fluffyfreak/tf330/rtl/ata.v

`timescale 1ns / 1ps
/*
    Copyright (C) 2016-2017, Stephen J. Leary
    All rights reserved.
    
    This file is part of  TF530 (Terrible Fire 030 Accelerator).

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
    You should have received a copy of the GNU General Public License
    along with TF530. If not, see <http://www.gnu.org/licenses/>.
*/

module ata (
           input         CLK,
           input         AS,
           input         RW,
           input [31:0] A,
           input        WAIT,

           output [1:0] IDECS,
           output        IOR,
           output        IOW,
           output   DTACK,
           output        ACCESS

       );

/* Timing Diagram
                 S0 S1 S2 S3 S4 S5  W  W S6 S7
     __    __    __    __    __    __    __    __    __    __    __    __   
CLK |  |__|  |__|  |__|  |__|  |__|  |__|  |__|  |__|  |__|  |__|  |__|  |__
     _________________                         _____________________________
AS                    \\\_____________________/
    _______________                            _____________________________
CS                 \__________________________/
    ______________________                     _____________________________
IOR                       \___________________/
    _____________________________        ___________________________________
IOW                              \______/
    _____________________________        ___________________________________
DTACK                            \______/     
    _________________________       ________________________________________
WAIT                         \_____/
        
*/

// decode directly from AS and Address Bus.
wire GAYLE_IDE = ({A[31:15]} != {16'h00DA,1'b0});

reg ASDLY = 1'b1;
reg ASDLY2 = 1'b1;
reg DTACK_INT = 1'b1;

reg IOR_INT = 1'b1;
reg IOW_INT = 1'b1;

always @(posedge CLK or posedge AS) begin

    if (AS == 1'b1) begin

        ASDLY <= 1'b1;
        ASDLY2 <= 1'b1;

    end else begin

        ASDLY <= AS;
        ASDLY2 <= ASDLY;

    end

end

always @(negedge CLK or posedge AS) begin

    if (AS == 1'b1) begin

        IOR_INT <= 1'b1;
        IOW_INT <= 1'b1;
        DTACK_INT <= 1'b1;

    end else begin

        IOR_INT <= ~RW | ASDLY | GAYLE_IDE;
        IOW_INT <=  RW | ASDLY2 | GAYLE_IDE;
        DTACK_INT <=  ASDLY2 | GAYLE_IDE;

    end

end

assign IOR = IOR_INT;
assign IOW = IOW_INT ;
assign DTACK = DTACK_INT;

assign IDECS = A[12] ? {GAYLE_IDE, 1'b1} : {1'b1, GAYLE_IDE};
assign ACCESS = GAYLE_IDE;


endmodule
